AravinthPanch/swan-lake-music-art/hardware/attiny85-breakout/attiny85-breakout.sch

## KiCad design hardware/attiny85-breakout/attiny85-breakout.sch (2017-01-16)

Schematic: attiny85-breakout.sch

Parts:
IC1: ATTINY85-S; SOIJ-8_5.3x5.3mm_Pitch1.27mm
P1: CONN_01X08; Pin_Header_Straight_1x08_Pitch2.54mm
