AravinthPanch/swan-lake-music-art/key_frequency.h

/*******************************************************************************
*
*    @file     key_frequency.h
*    @brief    Piano key frequencies with the 49th key, the fifth A (A4), tuned to 440 Hz.
*              Key frequencies are rounded.
*
********************************************************************************/

#ifndef _KEY_FREQUENCY_H_
#define _KEY_FREQUENCY_H_

// 3rd Octave
#define C3 		(130)
#define Cx3		(138)
#define D3		(146)
#define Dx3		(155)
#define E3		(164)
#define F3		(174)
#define Fx3		(184)
#define G3		(195)
#define Gx3		(207)
#define A3		(220)
#define Ax3		(233)
#define B3		(246)

// 4th Octave
#define C4 		(261)
#define Cx4		(277)
#define D4		(293)
#define Dx4		(311)
#define E4		(329)
#define F4		(349)
#define Fx4		(369)
#define G4		(391)
#define Gx4		(415)
#define A4		(440)
#define Ax4		(466)
#define B4		(493)

// 5th Octave
#define C5 		(523)
#define Cx5		(554)
#define D5		(587)
#define Dx5		(622)
#define E5		(659)
#define F5		(698)
#define Fx5		(739)
#define G5		(783)
#define Gx5		(830)
#define A5		(880)
#define Ax5		(932)
#define B5		(987)

// 6th Octave
#define C6 		(1046)
#define Cx6		(1108)
#define D6		(1174)
#define Dx6		(1244)
#define E6		(1318)
#define F6		(1396)
#define Fx6		(1479)
#define G6		(1567)
#define Gx6		(1661)
#define A6		(1760)
#define Ax6		(1864)
#define B6		(1975)

#endif /*_KEY_FREQUENCY_H_*/
